g-goessel/TIPE-RFID/acquisitions/Capture du 2014-12-05 14:53:10.png

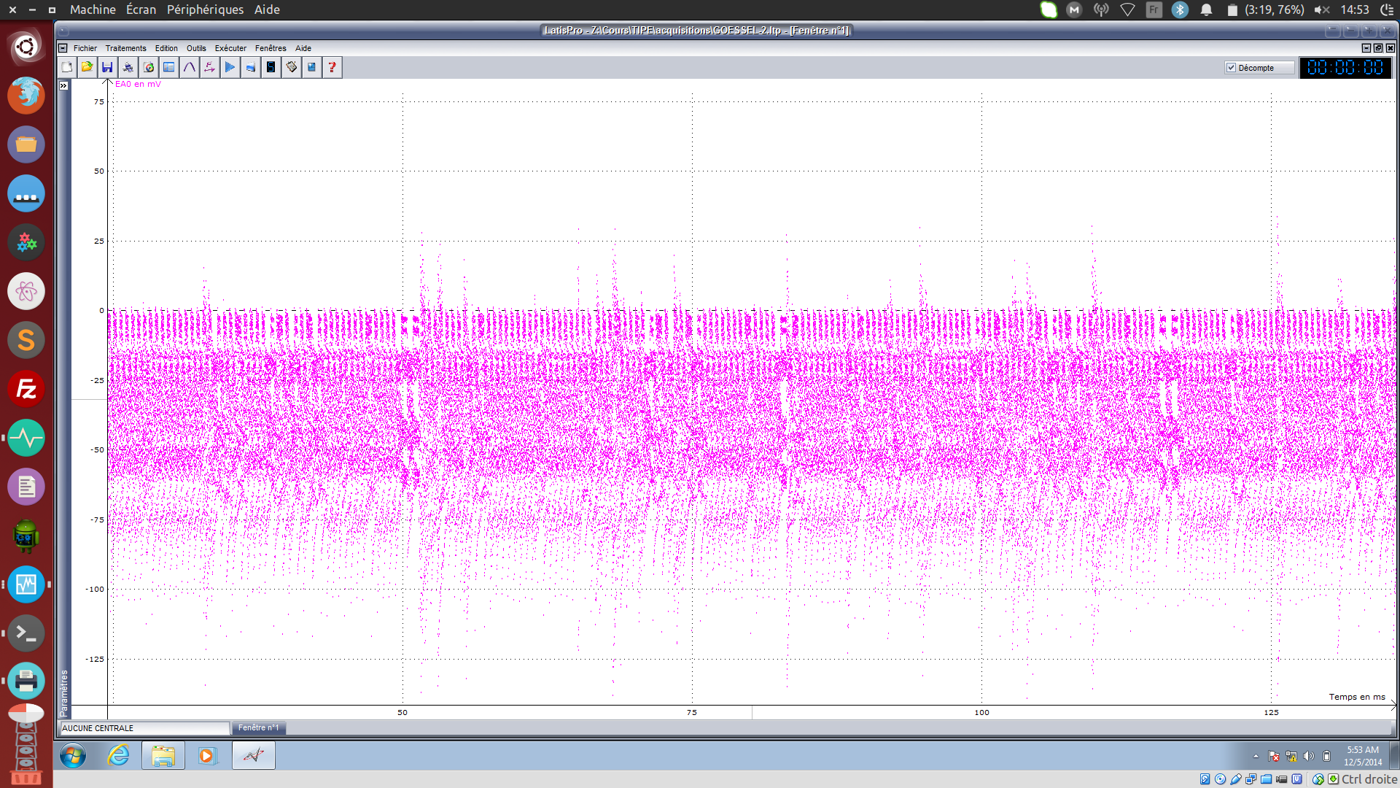
acquisitions/Capture du 2014-12-05 14:53:10.png
