g-goessel/TIPE-RFID/acquisitions/GOESSEL - 2.png

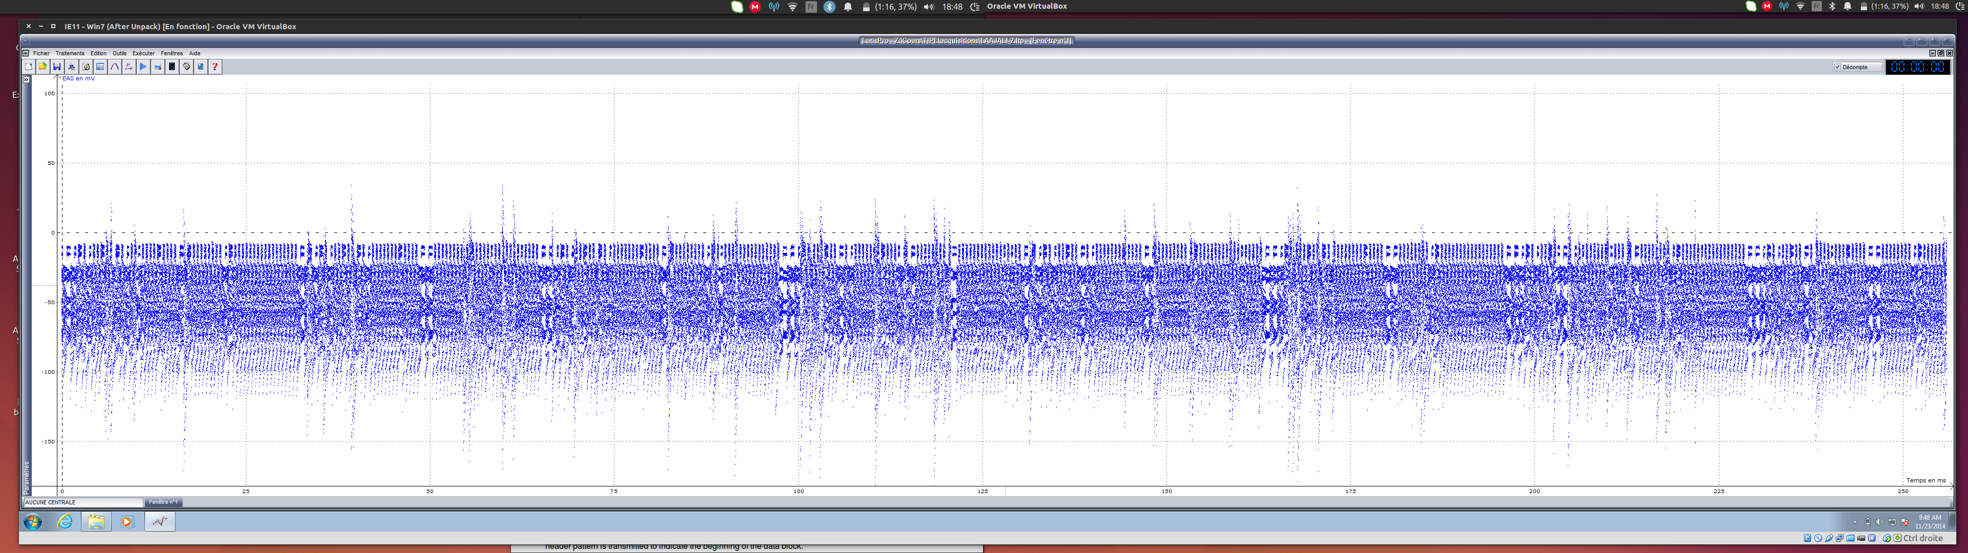
acquisitions/GOESSEL - 2.png
