g-goessel/TIPE-RFID/acquisitions/GOESSEL.png

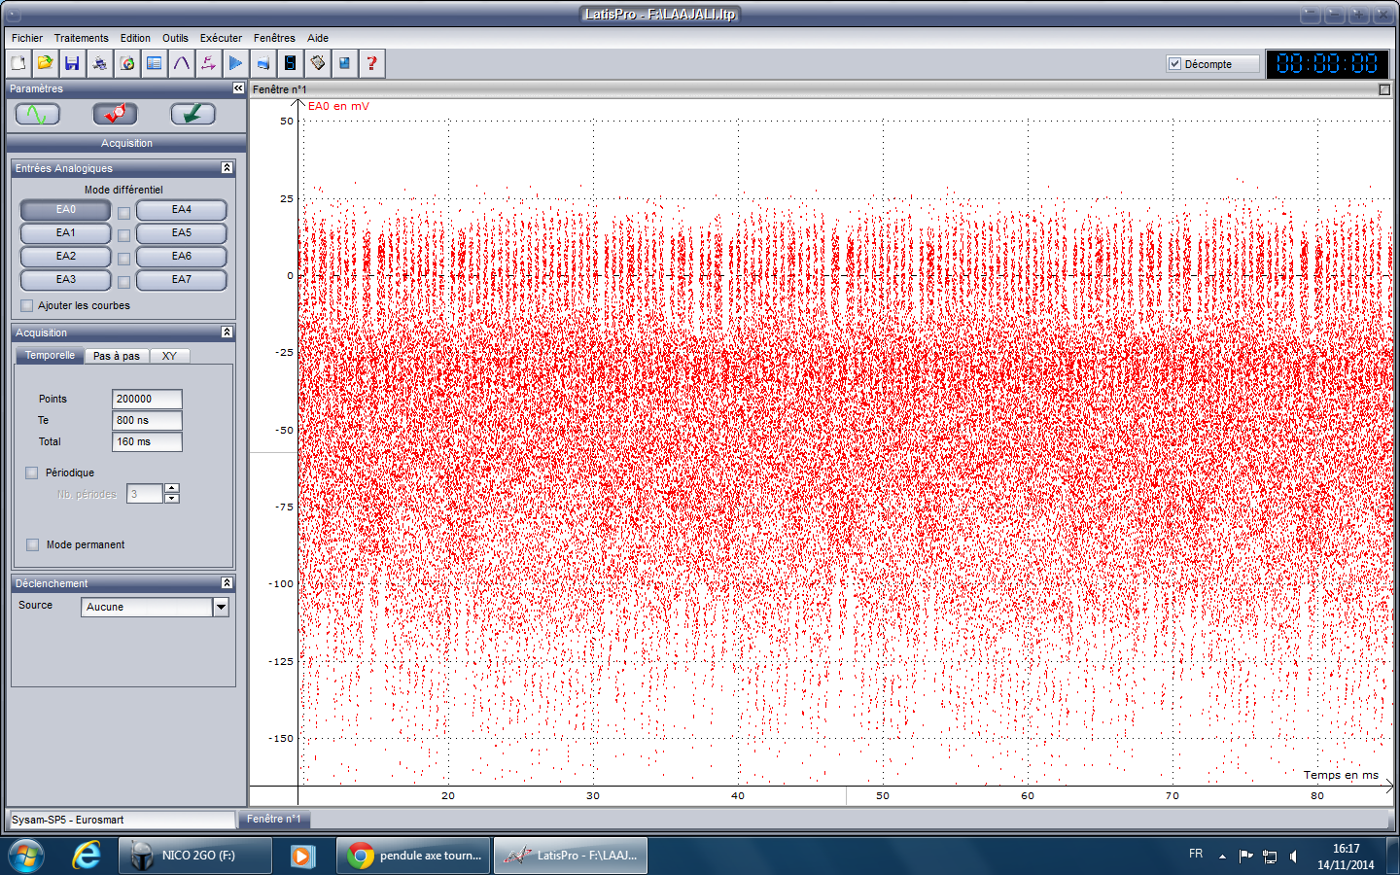
acquisitions/GOESSEL.png
