g-goessel/TIPE-RFID/Photos/IMG_20150410_160246.jpg

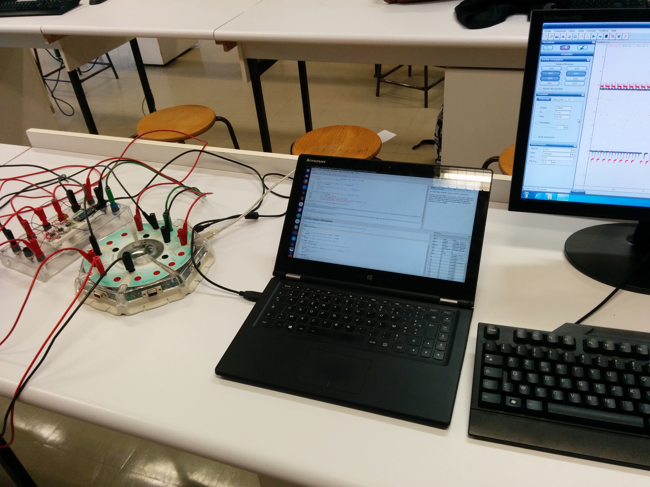
Photos/IMG_20150410_160246.jpg
