g-goessel/TIPE-RFID/Photos/IMG_20150410_160251.jpg

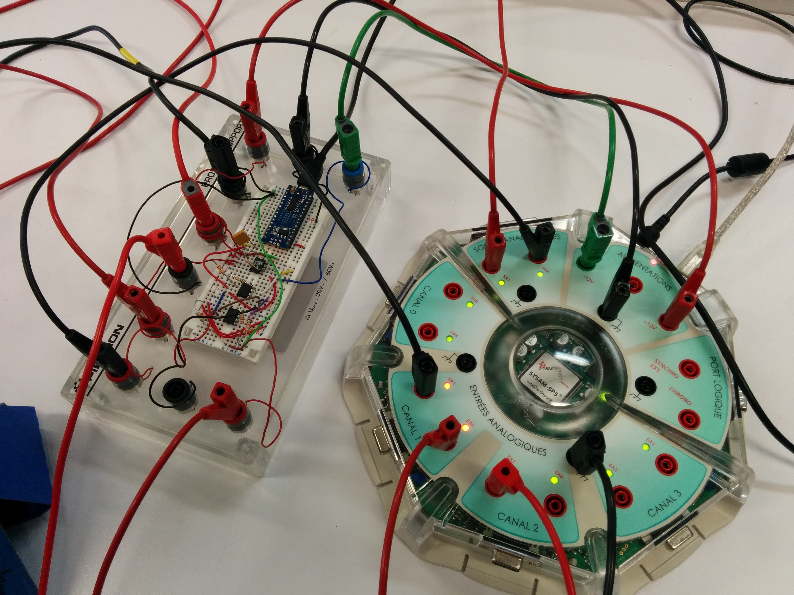
Photos/IMG_20150410_160251.jpg
