g-goessel/TIPE-RFID/Photos/IMG_20150517_205552.jpg

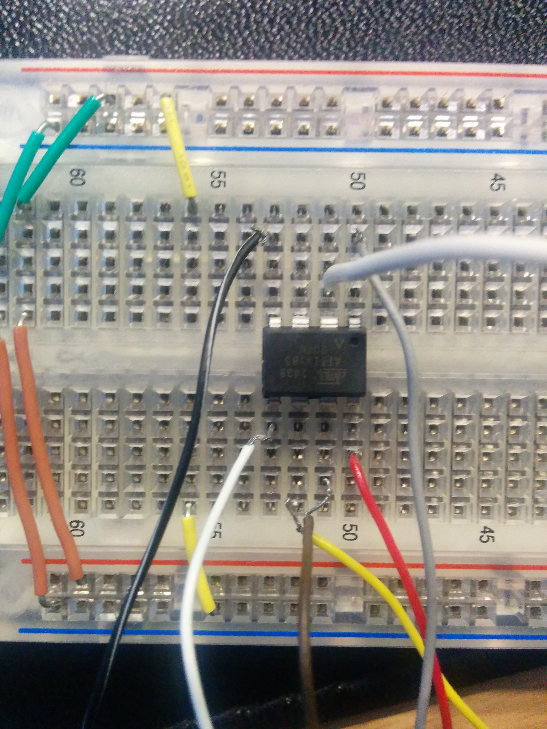
Photos/IMG_20150517_205552.jpg
