g-goessel/TIPE-RFID/Photos/IMG_20150517_205557.jpg

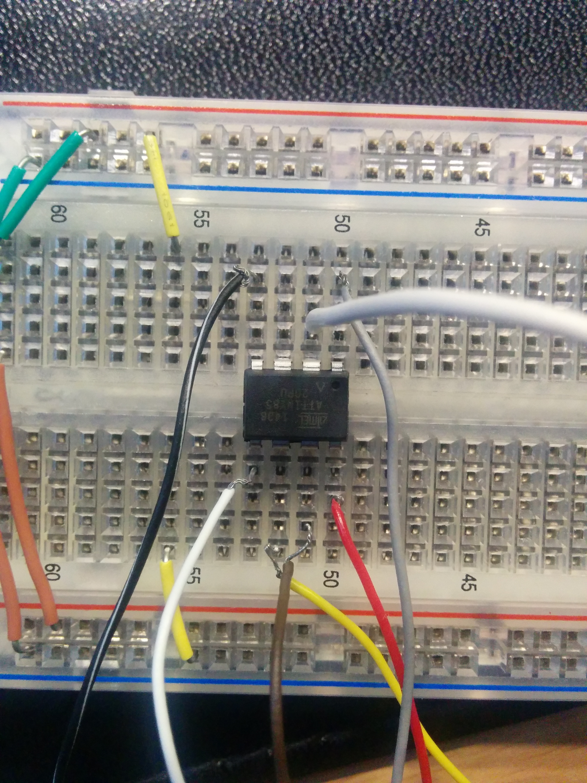
Photos/IMG_20150517_205557.jpg
