g-goessel/TIPE-RFID/Photos/IMG_20150519_115045.jpg

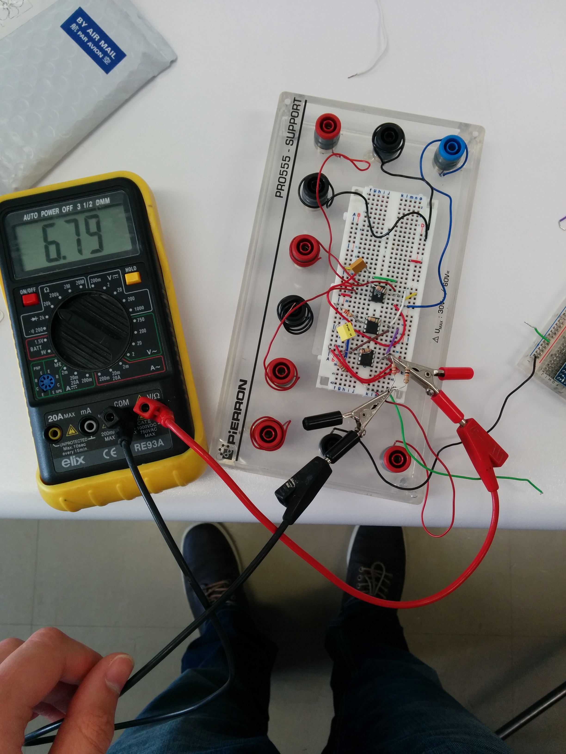
Photos/IMG_20150519_115045.jpg
