g-goessel/TIPE-RFID/Photos/IMG_20150519_115102.jpg

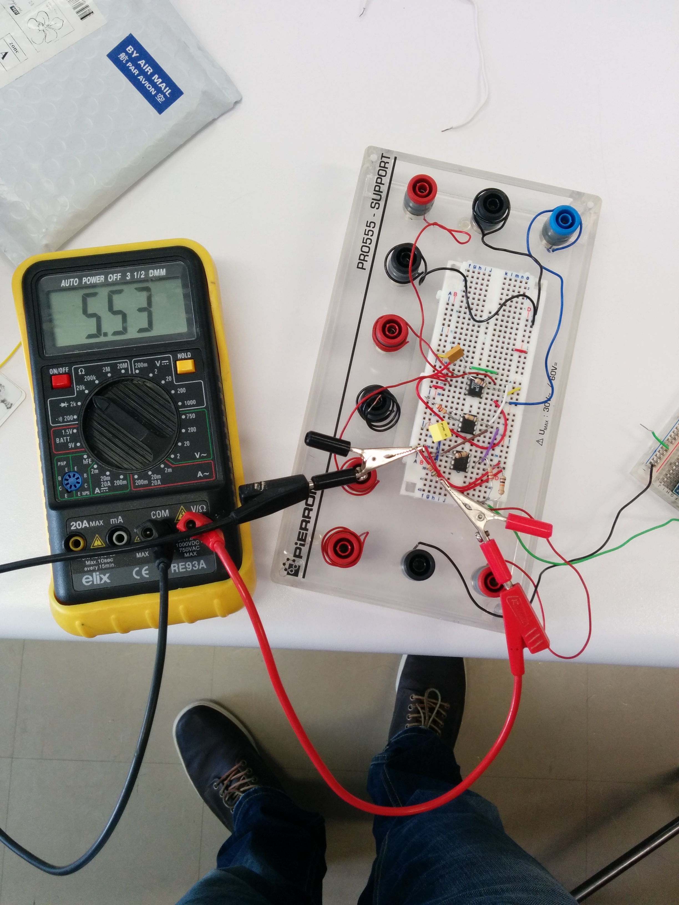
Photos/IMG_20150519_115102.jpg
