g-goessel/TIPE-RFID/Photos/IMG_20150519_115138.jpg

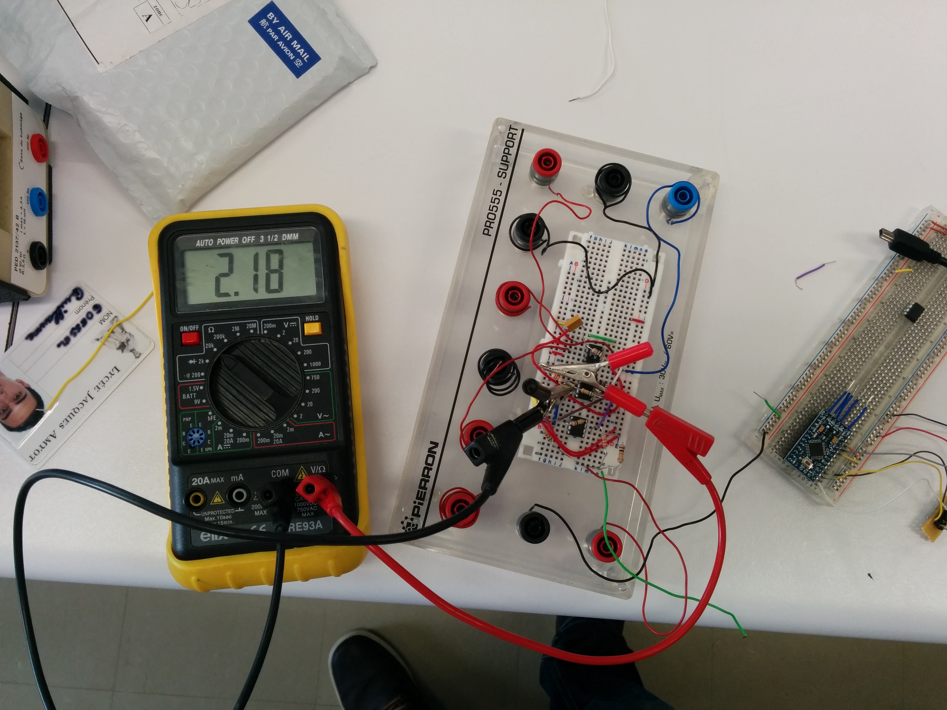
Photos/IMG_20150519_115138.jpg
