g-goessel/TIPE-RFID/Photos/IMG_20150519_115236.jpg

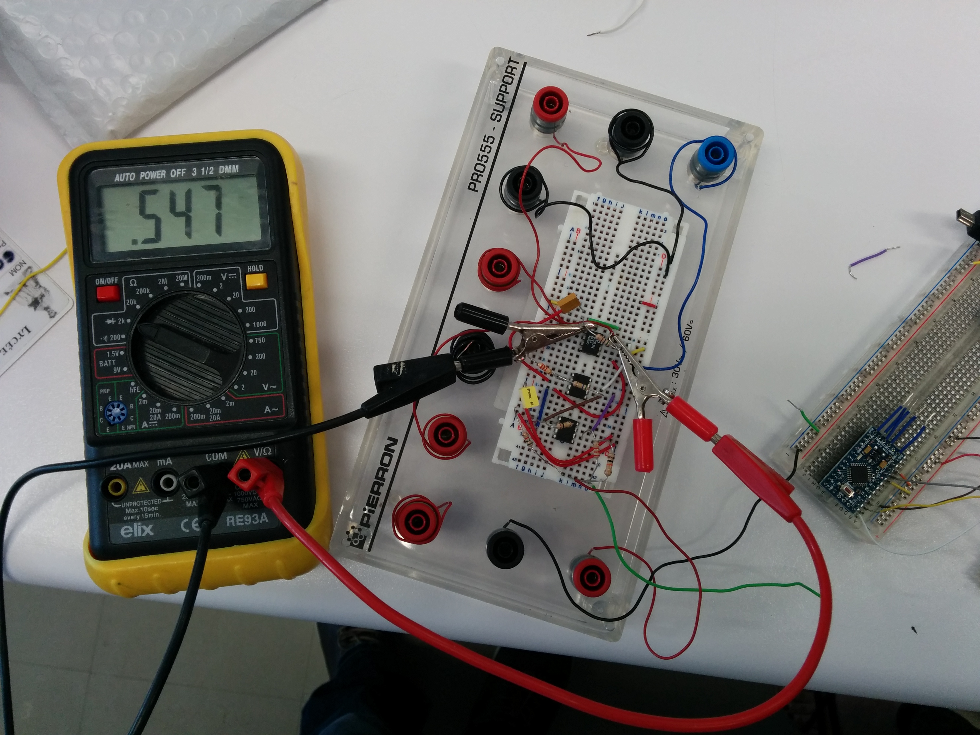
Photos/IMG_20150519_115236.jpg
