g-goessel/TIPE-RFID/Transparents/avant ampli.png

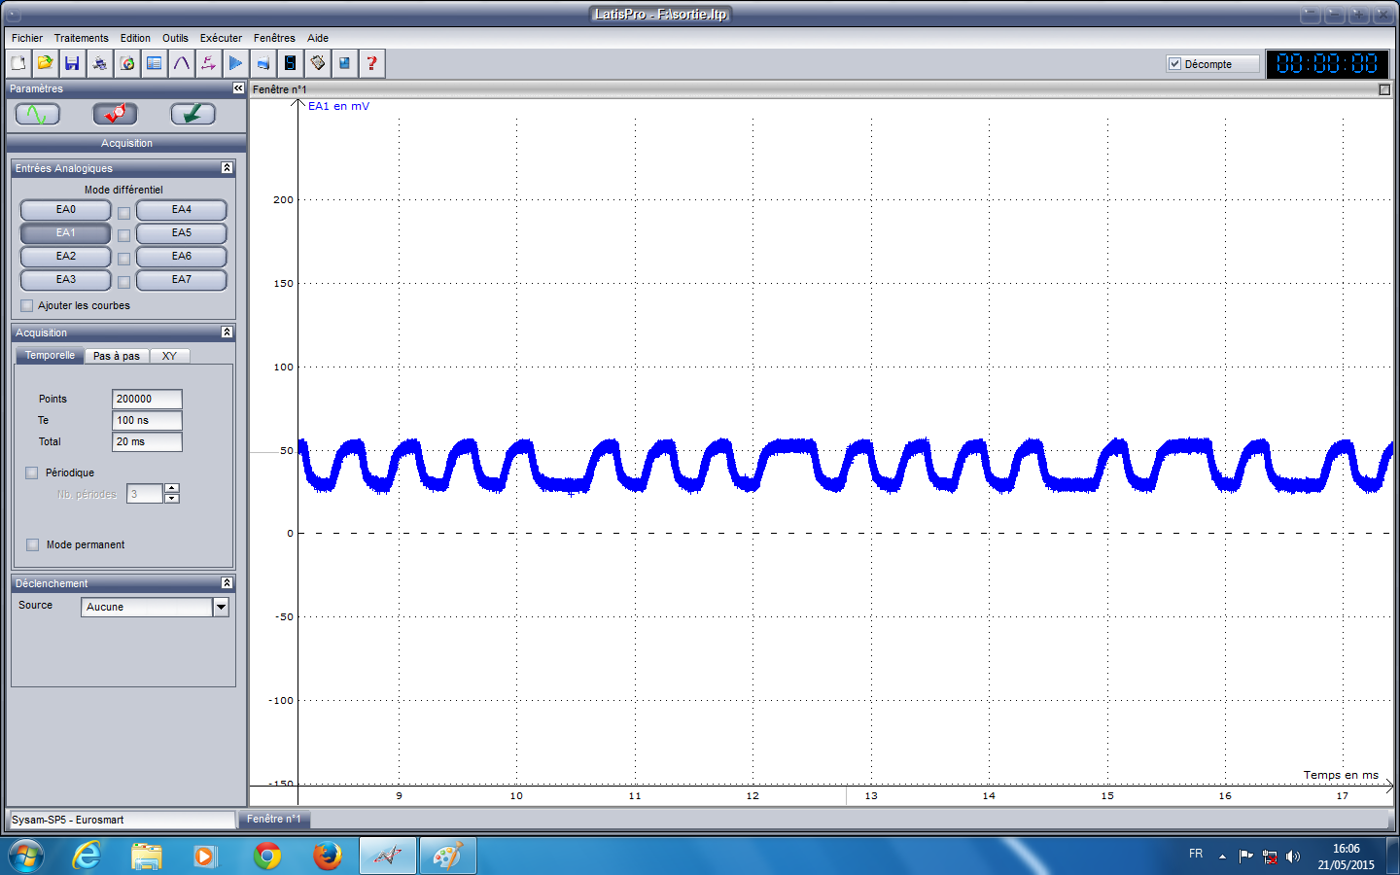
Transparents/avant ampli.png
