g-goessel/TIPE-RFID/Transparents/avant comparateur 2 .png

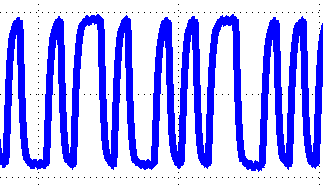
Transparents/avant comparateur 2 .png
