g-goessel/TIPE-RFID/Transparents/avant comparateur.png

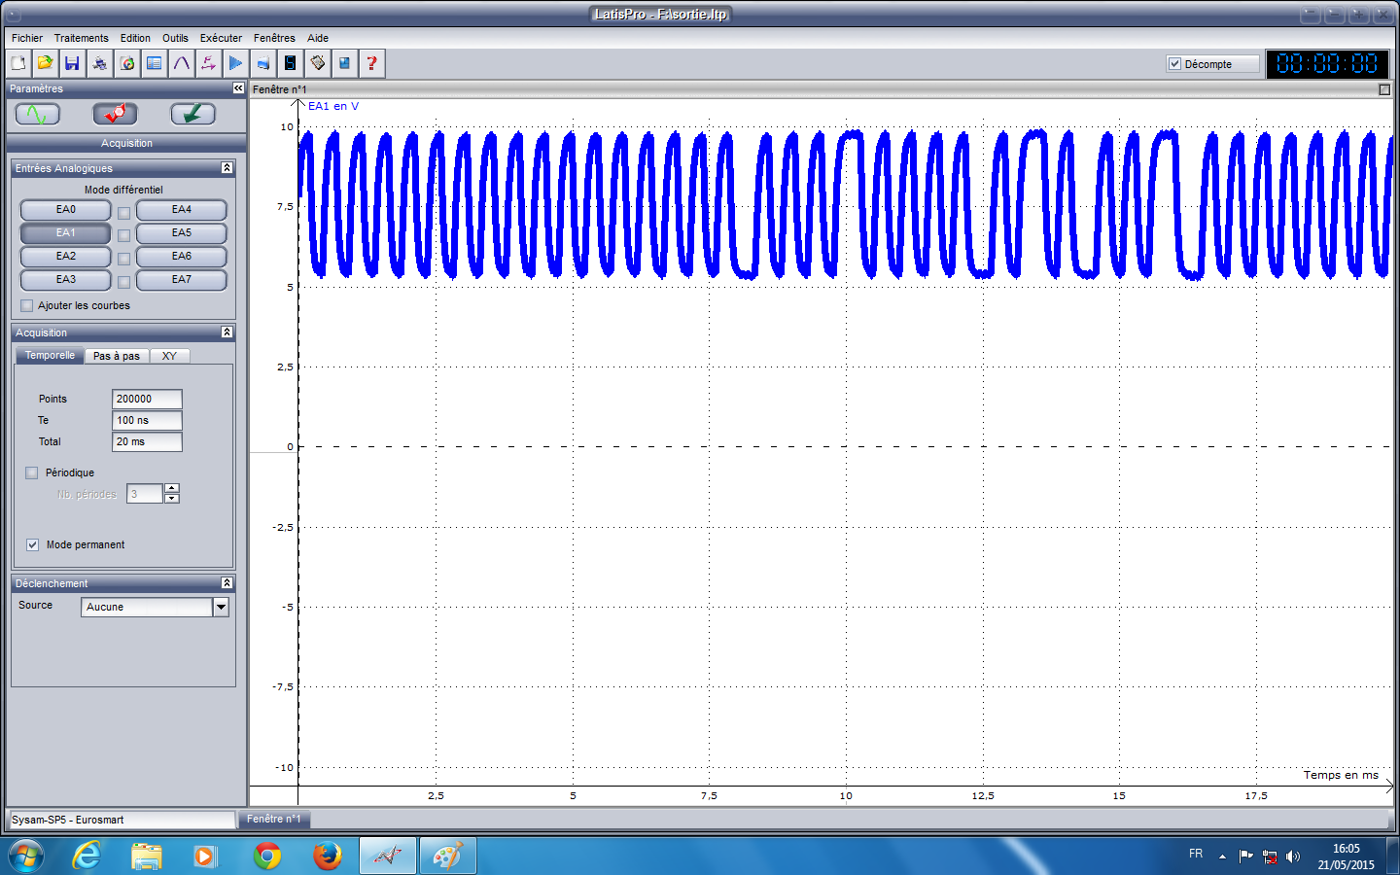
Transparents/avant comparateur.png
