g-goessel/TIPE-RFID/Transparents/avant RC.png

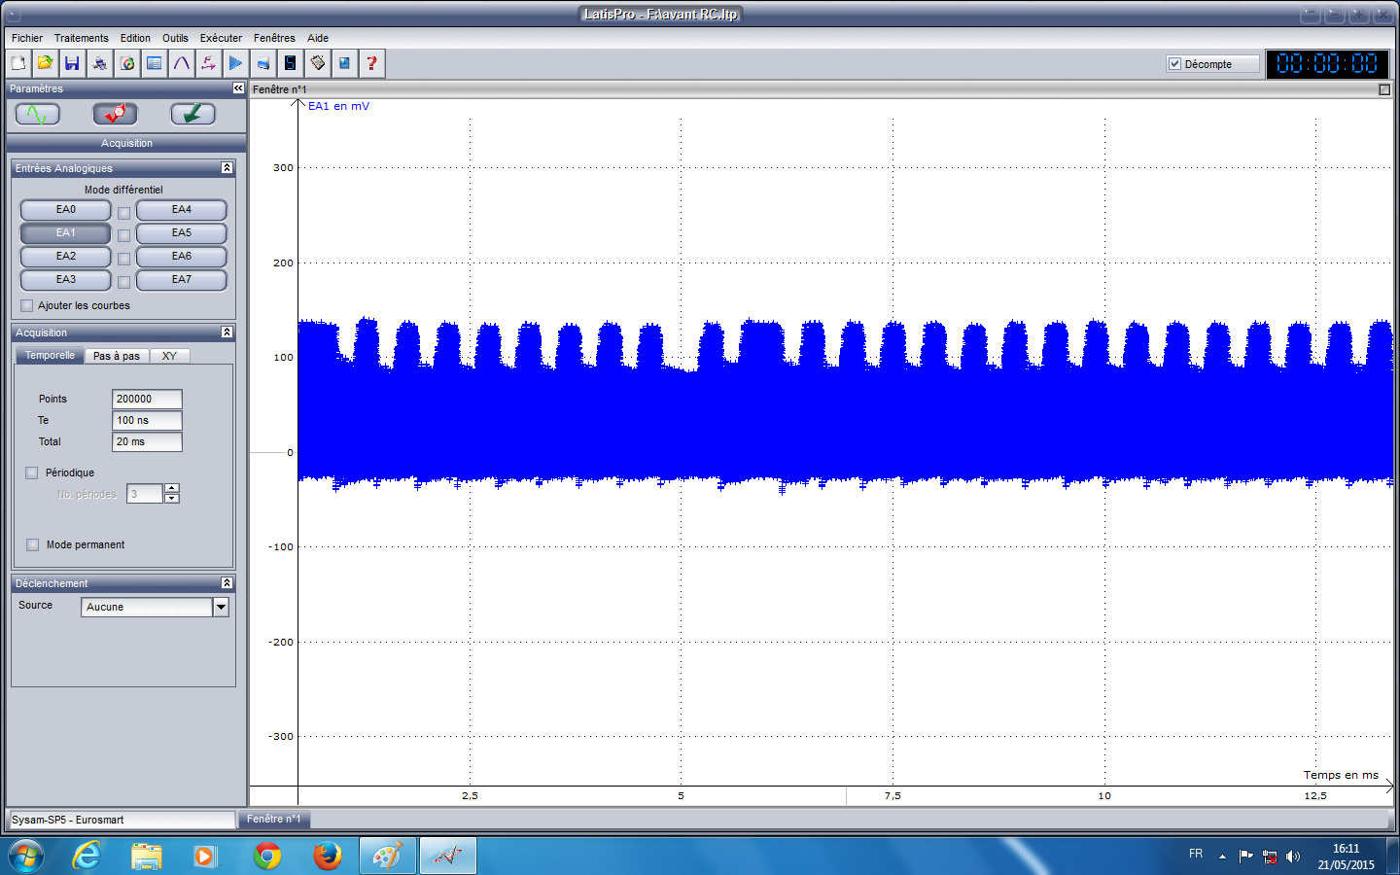
Transparents/avant RC.png
