g-goessel/TIPE-RFID/Transparents/bit.png

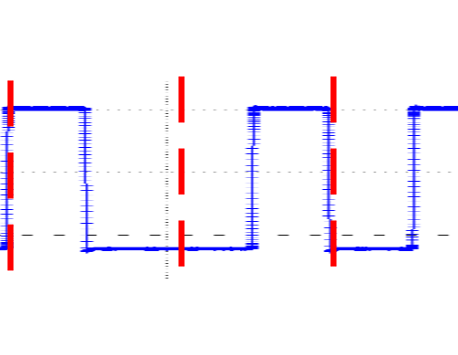
Transparents/bit.png
