g-goessel/TIPE-RFID/Transparents/Capture du 2015-05-25 22:49:48.png

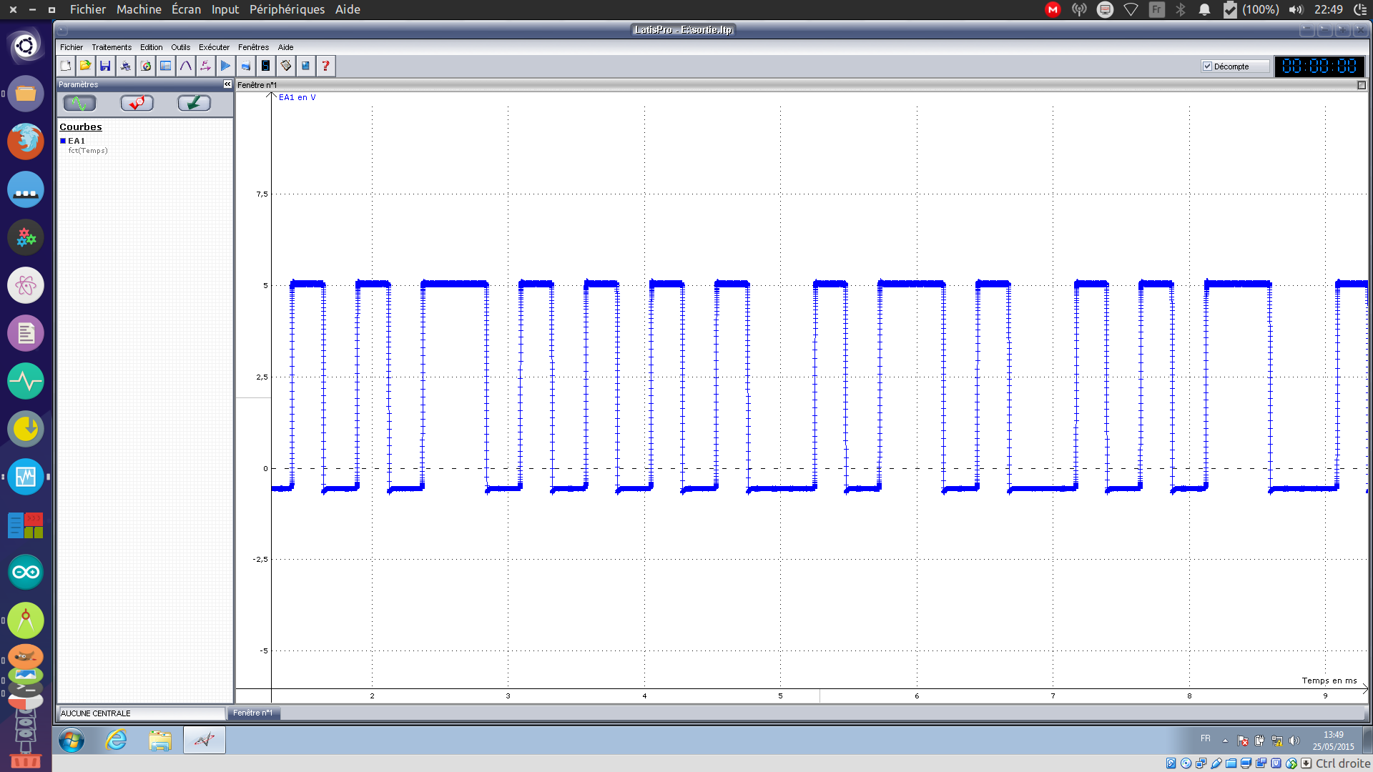
Transparents/Capture du 2015-05-25 22:49:48.png
