g-goessel/TIPE-RFID/Transparents/Document numérisé-01.jpg

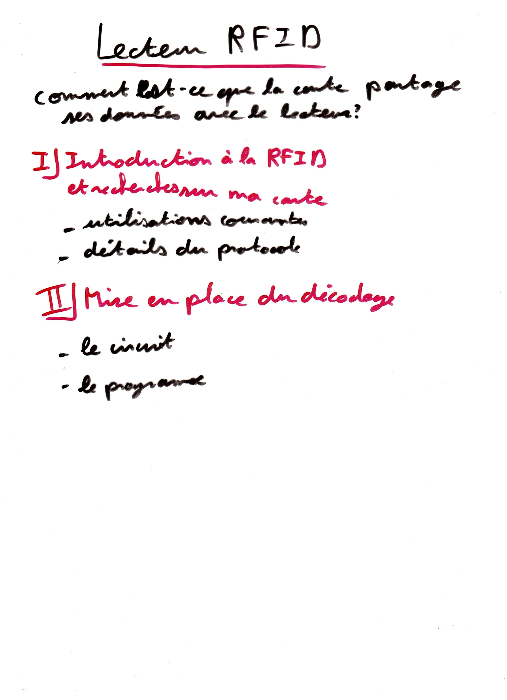
Transparents/Document numérisé-01.jpg
