g-goessel/TIPE-RFID/Transparents/Document numérisé-02.jpg

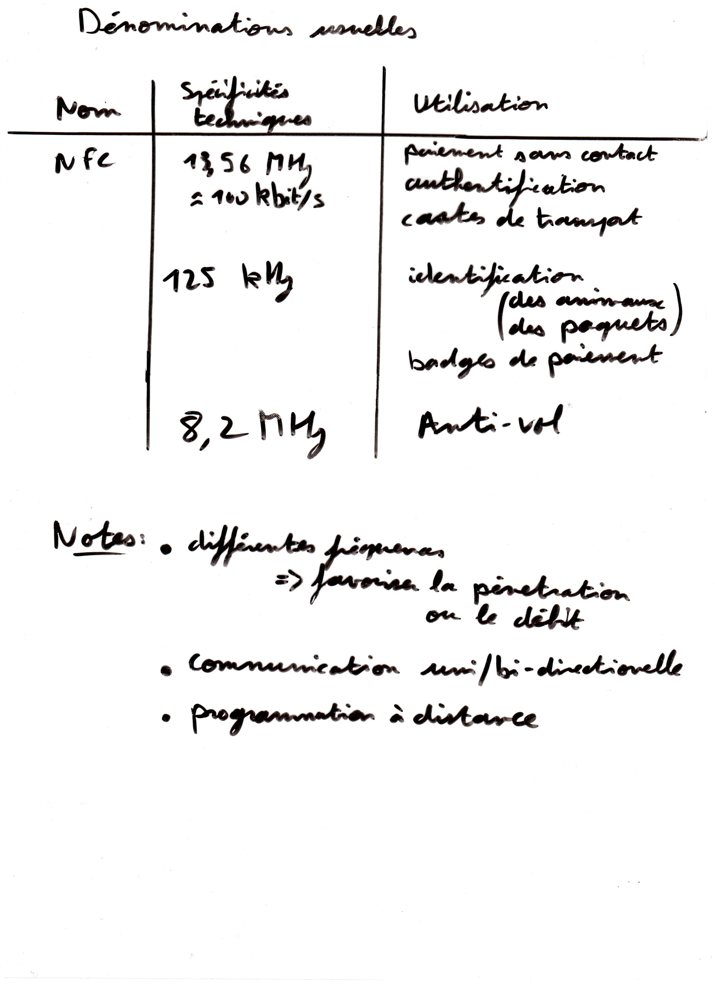
Transparents/Document numérisé-02.jpg
