g-goessel/TIPE-RFID/Transparents/Document numérisé-03.jpg

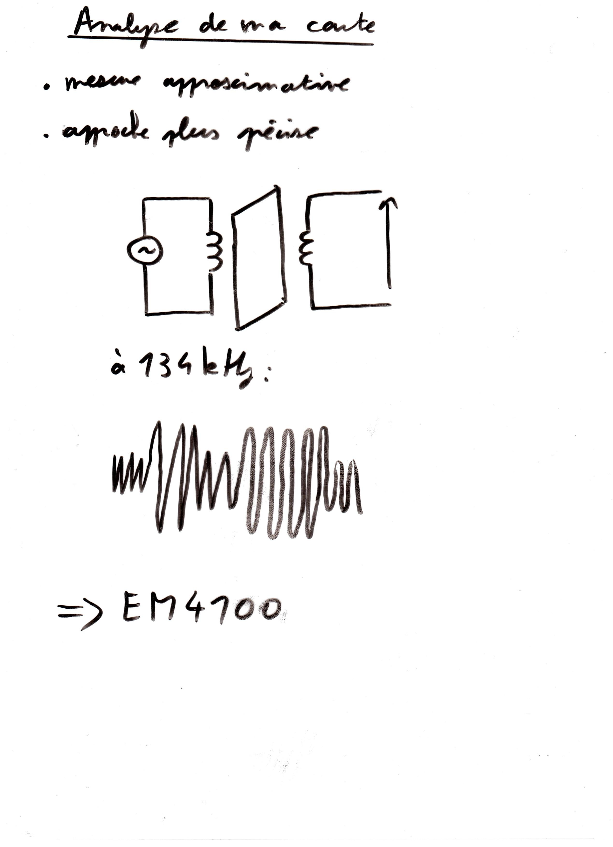
Transparents/Document numérisé-03.jpg
