g-goessel/TIPE-RFID/Transparents/Document numérisé-04-2.png

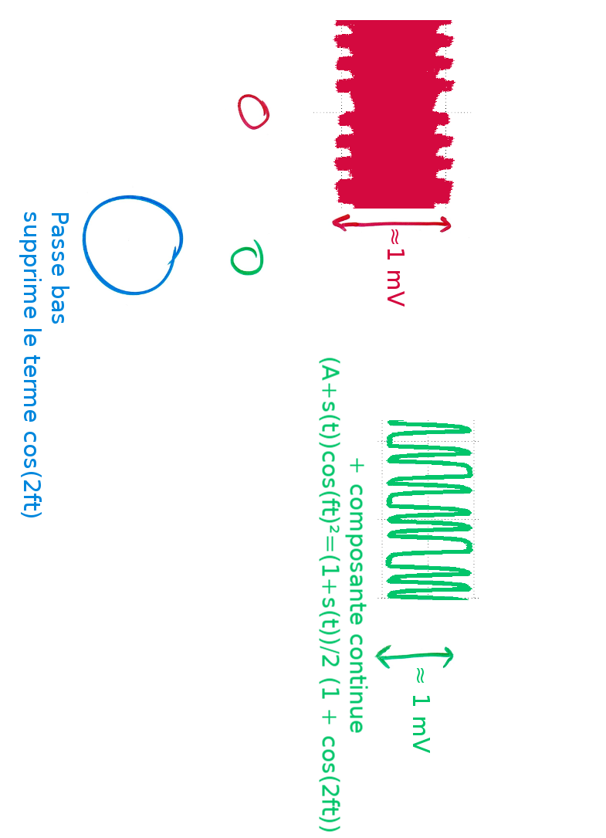
Transparents/Document numérisé-04-2.png
