g-goessel/TIPE-RFID/Transparents/Document numérisé-05-2.png

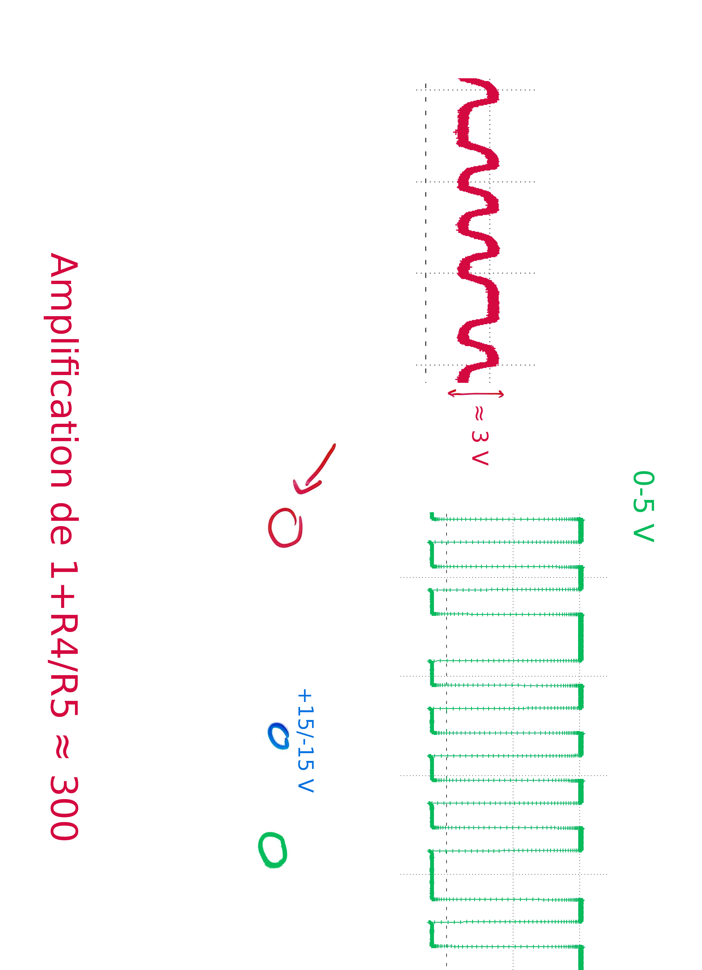
Transparents/Document numérisé-05-2.png
