g-goessel/TIPE-RFID/Transparents/Document numérisé-05.jpg

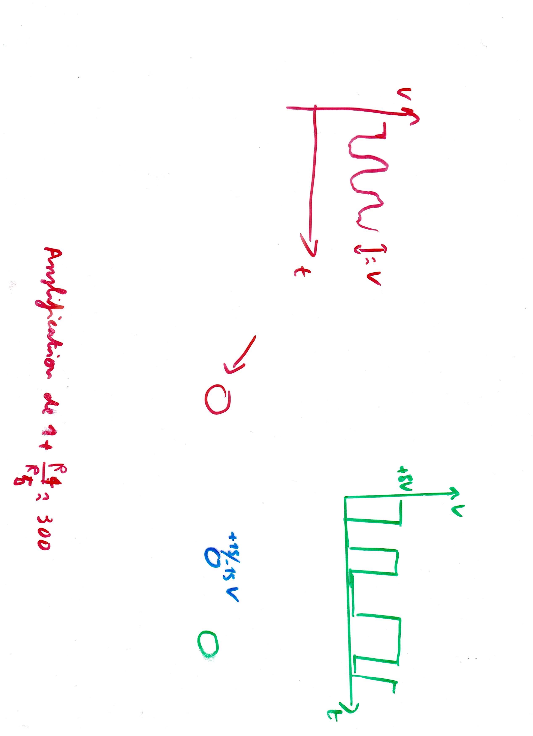
Transparents/Document numérisé-05.jpg
