g-goessel/TIPE-RFID/Transparents/Document numérisé-06.jpg

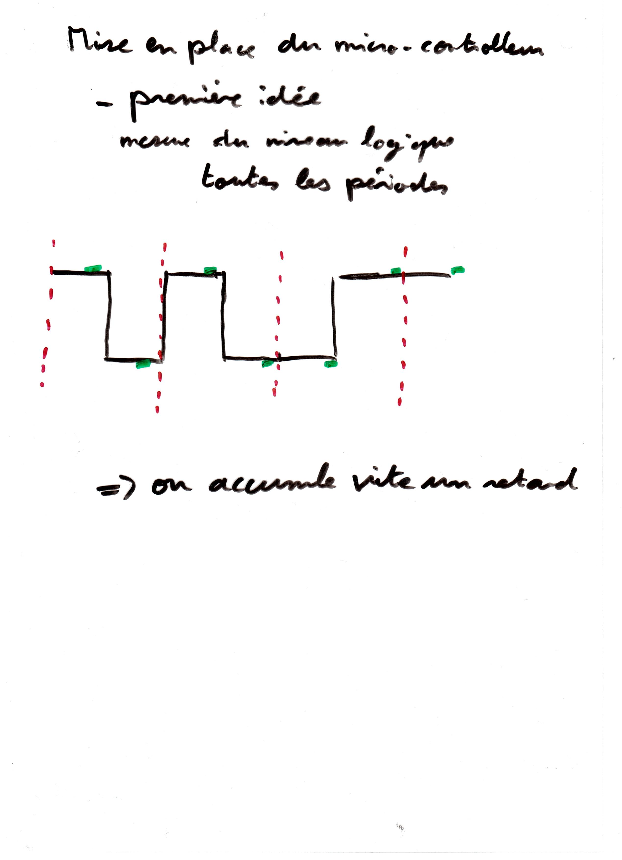
Transparents/Document numérisé-06.jpg
