g-goessel/TIPE-RFID/Transparents/Document numérisé-08.jpg

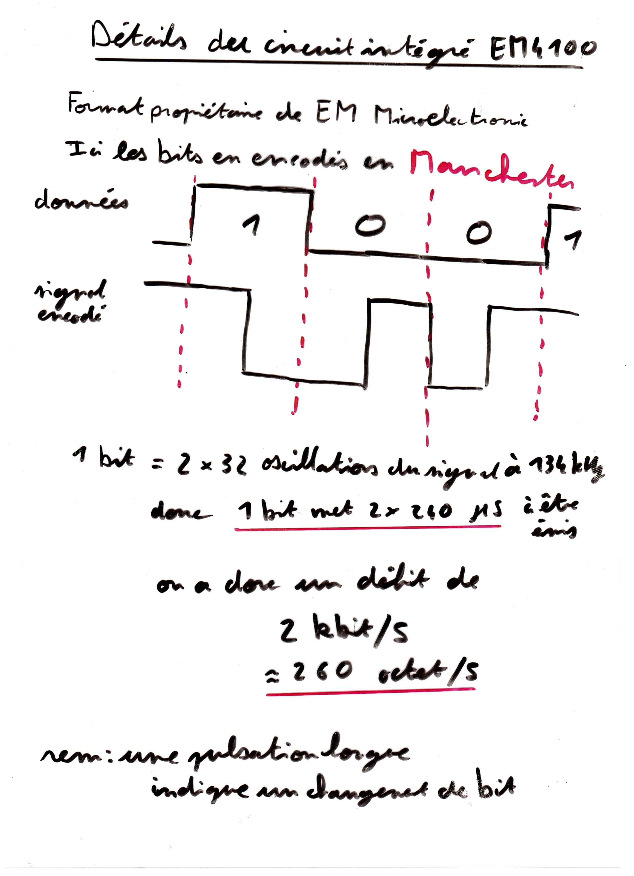
Transparents/Document numérisé-08.jpg
