g-goessel/TIPE-RFID/Transparents/Document numérisé-09.jpg

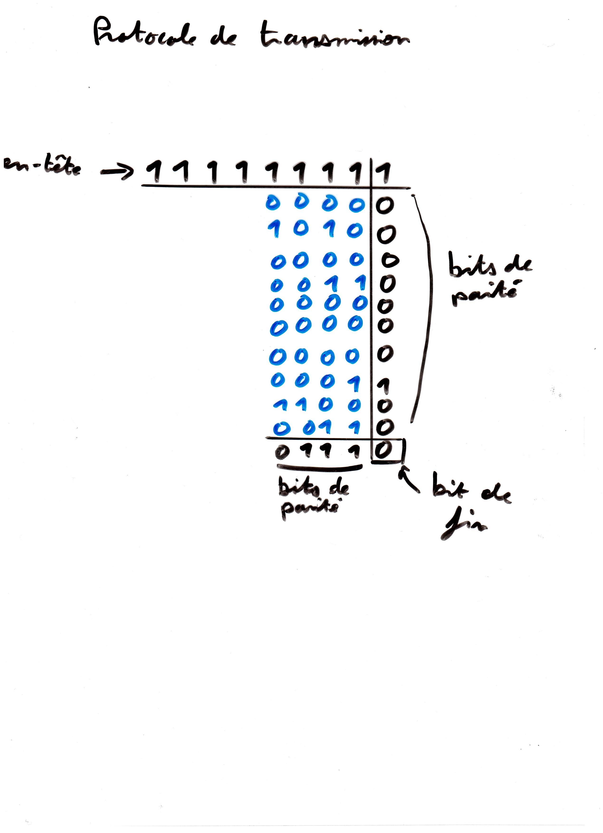
Transparents/Document numérisé-09.jpg
