g-goessel/TIPE-RFID/Transparents/Document numérisé-10.jpg

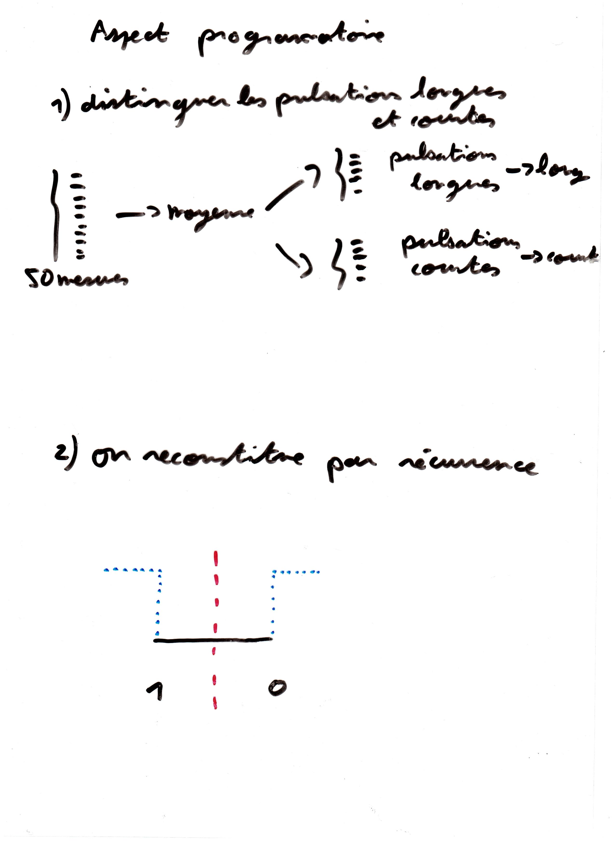
Transparents/Document numérisé-10.jpg
