g-goessel/TIPE-RFID/Transparents/Document numérisé-12.jpg

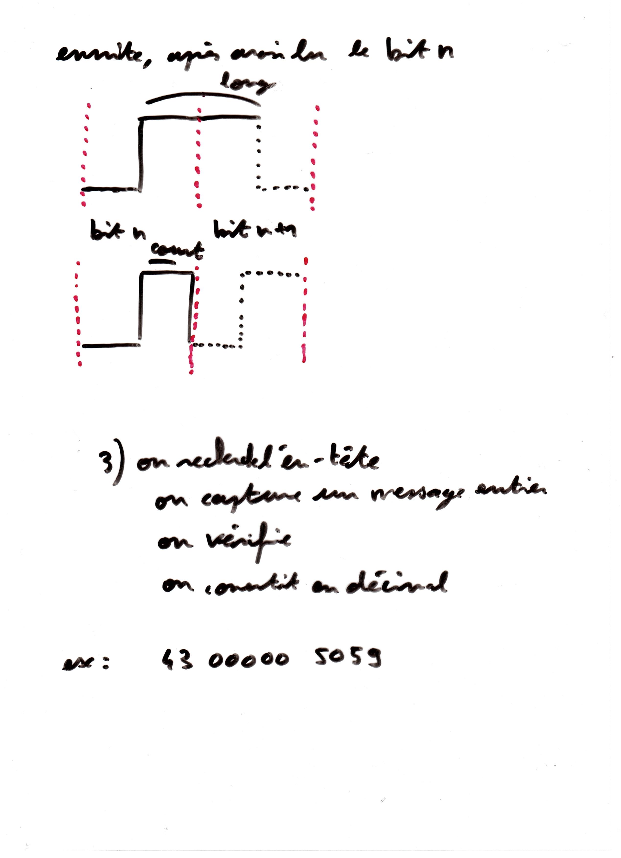
Transparents/Document numérisé-12.jpg
