g-goessel/TIPE-RFID/Transparents/Document numérisé-13.jpg

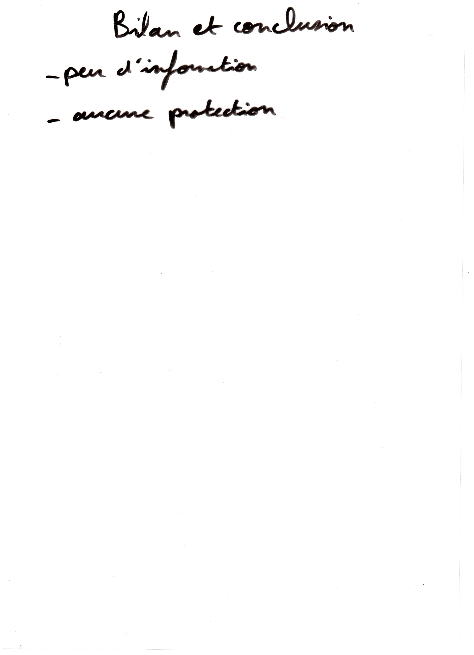
Transparents/Document numérisé-13.jpg
