g-goessel/TIPE-RFID/Transparents/sortie bobine.png

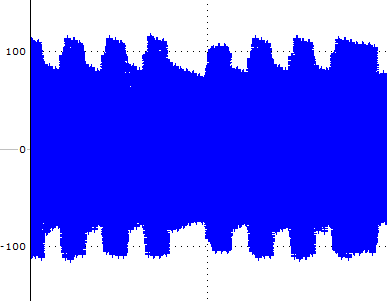
Transparents/sortie bobine.png
