g-goessel/TIPE-RFID/Transparents/sortie.png

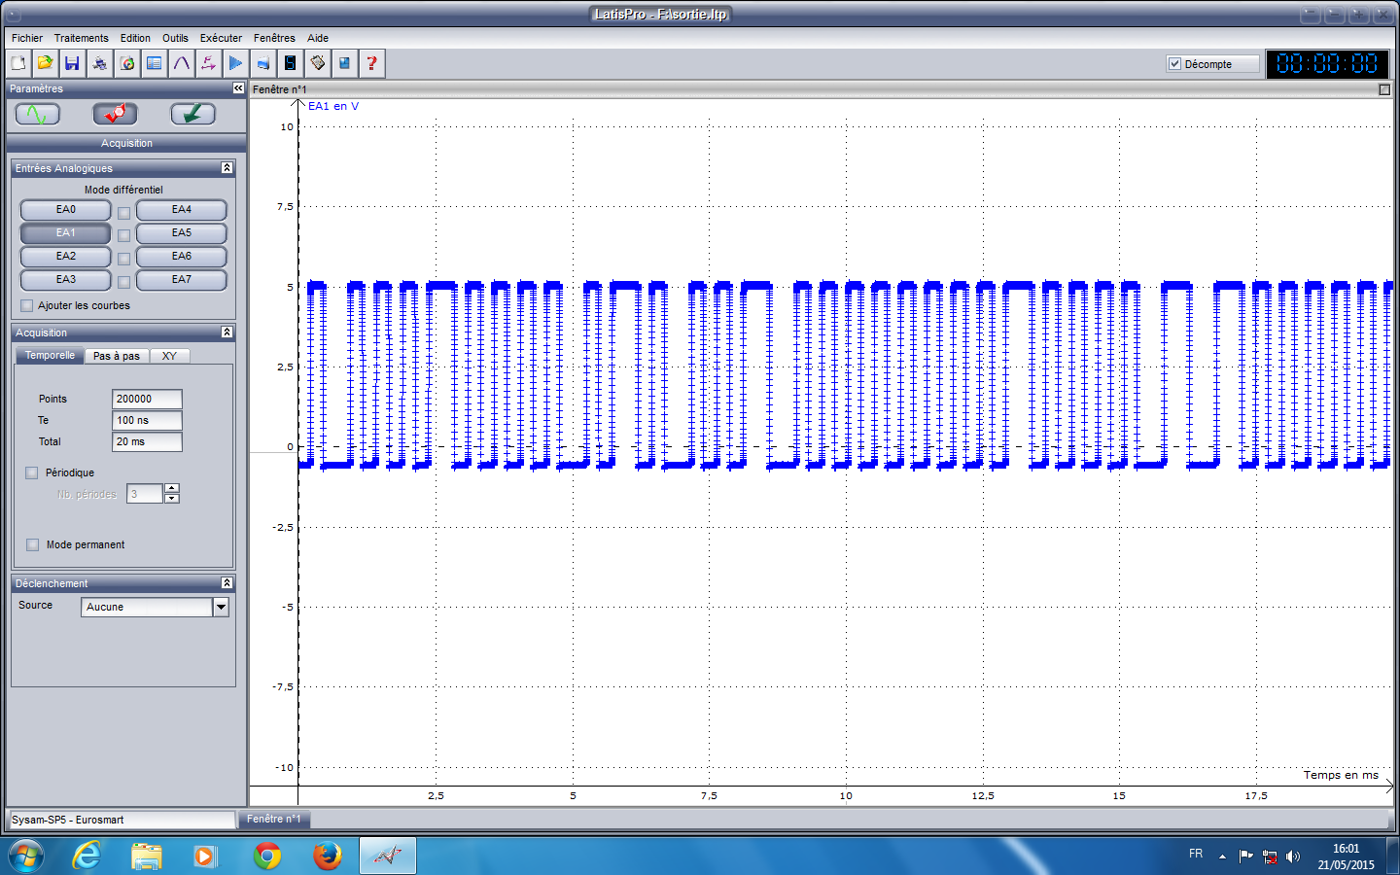
Transparents/sortie.png
